AkramHourani/MapperBot/HardwareDesign/Schematic/slamcAR01.sch

## EAGLE design HardwareDesign/Schematic/slamcAR01.sch (2019-04-01)

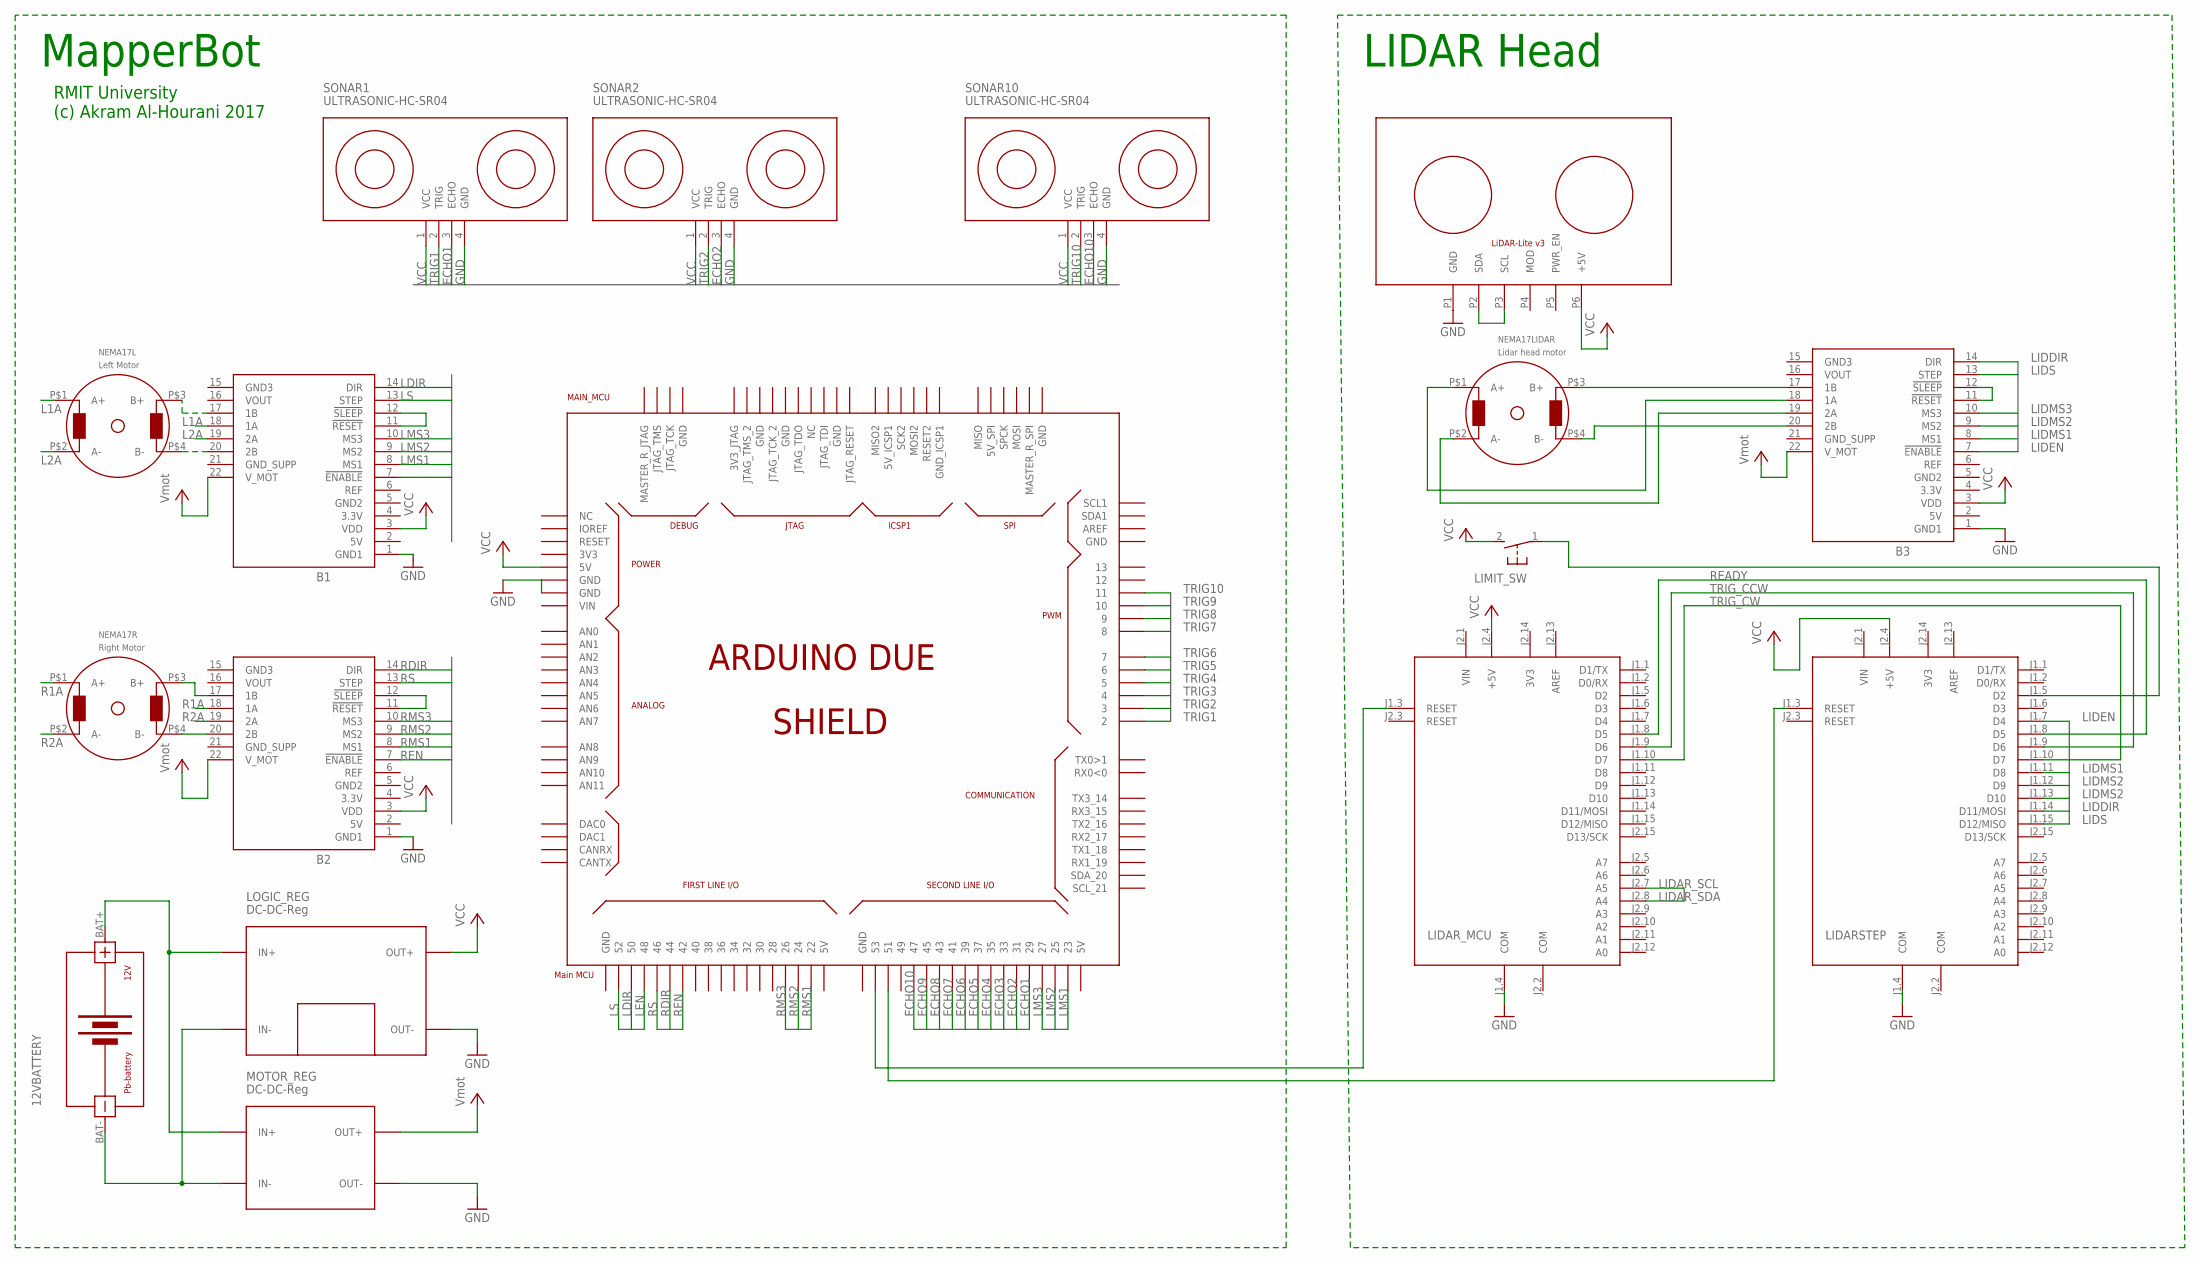
[picture p2: schematic slamcAR01.sch]

Parts:
12VBATTERY: BATTERY-LI-MH12210
B1, B2, B3: POLOLU_1183
LIDARSTEP: ARDUINO_NANO2
LIDAR_MCU: ARDUINO_NANO2
LIMIT_SW: 31-XX; B3F-31XX
LOGIC_REG: DC-DC-Reg; DC-DC-LM2596-DISP
MAIN_MCU: Main MCU; ARDUINO_DUE_SHIELD
MOTOR_REG: DC-DC-Reg; DC-DC-STEP-DOWN-LM2596
NEMA17L: Left Motor; X25_168
NEMA17LIDAR: Lidar head motor; X25_168
NEMA17R: Right Motor; X25_168
SONAR1, SONAR2, SONAR10: ULTRASONIC-HC-SR04
U$6: LIDAR

Connections:
ECHO1: MAIN_MCU.29, SONAR1.3 (ECHO)
ECHO2: MAIN_MCU.31, SONAR2.3 (ECHO)
ECHO3: MAIN_MCU.33
ECHO4: MAIN_MCU.35
ECHO5: MAIN_MCU.37
ECHO6: MAIN_MCU.39
ECHO7: MAIN_MCU.41
ECHO8: MAIN_MCU.43
ECHO9: MAIN_MCU.45
ECHO10: MAIN_MCU.47, SONAR10.3 (ECHO)
GND: B2.1 (GND1), B3.1 (GND1), LIDARSTEP.J1.4 (COM), LIDAR_MCU.J1.4 (COM), LOGIC_REG.OUT-, MAIN_MCU.GND, MAIN_MCU.GND_1 (GND), MOTOR_REG.OUT-, SONAR1.4 (GND), SONAR2.4 (GND), SONAR10.4 (GND), U$6.P1 (GND)
L1A: B1.18 (1A), NEMA17L.P$1 (A+)
L2A: B1.19 (2A), NEMA17L.P$2 (A-)
LDIR: B1.14 (DIR), MAIN_MCU.50
LEN: B1.7 (!ENABLE), MAIN_MCU.48
LIDAR_SCL: LIDAR_MCU.J2.7 (A5)
LIDAR_SDA: LIDAR_MCU.J2.8 (A4), U$6.P2 (SDA), U$6.P3 (SCL)
LIDDIR: B3.14 (DIR), LIDARSTEP.J1.14 (D11/MOSI)
LIDEN: B3.7 (!ENABLE), LIDARSTEP.J1.7 (D4)
LIDMS1: B3.8 (MS1), LIDARSTEP.J1.11 (D8)
LIDMS2: B3.9 (MS2), LIDARSTEP.J1.12 (D9), LIDARSTEP.J1.13 (D10)
LIDMS3: B3.10 (MS3)
LIDS: B3.13 (STEP), LIDARSTEP.J1.15 (D12/MISO)
LMS1: B1.8 (MS1), MAIN_MCU.23
LMS2: B1.9 (MS2), MAIN_MCU.25
LMS3: B1.10 (MS3), MAIN_MCU.27
LS: B1.13 (STEP), MAIN_MCU.52
unnamed: B1.17 (1B), NEMA17L.P$3 (B+)
unnamed: B1.20 (2B), NEMA17L.P$4 (B-)
unnamed: B2.17 (1B), NEMA17R.P$3 (B+)
unnamed: B2.20 (2B), NEMA17R.P$4 (B-)
unnamed: B1.11 (!RESET), B1.12 (!SLEEP)
unnamed: B2.11 (!RESET), B2.12 (!SLEEP)
unnamed: LIDAR_MCU.J1.3 (RESET), MAIN_MCU.53
unnamed: LIDARSTEP.J1.3 (RESET), MAIN_MCU.51
unnamed: B3.17 (1B), NEMA17LIDAR.P$3 (B+)
unnamed: B3.20 (2B), NEMA17LIDAR.P$4 (B-)
unnamed: B3.19 (2A), NEMA17LIDAR.P$2 (A-)
unnamed: B3.18 (1A), NEMA17LIDAR.P$1 (A+)
unnamed: B3.11 (!RESET), B3.12 (!SLEEP)
unnamed: LIDARSTEP.J1.5 (D2), LIMIT_SW.1
unnamed: 12VBATTERY.BAT+, LOGIC_REG.IN+, MOTOR_REG.IN+
unnamed: 12VBATTERY.BAT-, LOGIC_REG.IN-, MOTOR_REG.IN-
R1A: B2.18 (1A), NEMA17R.P$1 (A+)
R2A: B2.19 (2A), NEMA17R.P$2 (A-)
RDIR: B2.14 (DIR), MAIN_MCU.44
READY: LIDARSTEP.J1.8 (D5), LIDAR_MCU.J1.8 (D5)
REN: B2.7 (!ENABLE), MAIN_MCU.42
RMS1: B2.8 (MS1), MAIN_MCU.22
RMS2: B2.9 (MS2), MAIN_MCU.24
RMS3: B2.10 (MS3), MAIN_MCU.26
RS: B2.13 (STEP), MAIN_MCU.46
TRIG1: MAIN_MCU.2, SONAR1.2 (TRIG)
TRIG2: MAIN_MCU.3, SONAR2.2 (TRIG)
TRIG3: MAIN_MCU.4
TRIG4: MAIN_MCU.5
TRIG5: MAIN_MCU.6
TRIG6: MAIN_MCU.7
TRIG7: MAIN_MCU.8
TRIG8: MAIN_MCU.9
TRIG9: MAIN_MCU.10
TRIG10: MAIN_MCU.11, SONAR10.2 (TRIG)
TRIG_CCW: LIDARSTEP.J1.9 (D6), LIDAR_MCU.J1.9 (D6)
TRIG_CW: LIDARSTEP.J1.10 (D7), LIDAR_MCU.J1.10 (D7)
VCC: B1.3 (VDD), B1.22 (V_MOT), B2.3 (VDD), B2.22 (V_MOT), B3.3 (VDD), B3.22 (V_MOT), LIDARSTEP.J2.4 (+5V), LIDAR_MCU.J2.4 (+5V), LIMIT_SW.2 (S), LOGIC_REG.OUT+, MAIN_MCU.5V0 (5V), MOTOR_REG.OUT+, SONAR1.1 (VCC), SONAR2.1 (VCC), SONAR10.1 (VCC), U$6.P6 (+5V)

Notes on the sheet:
MapperBot
RMIT University (c) Akram Al-Hourani 2017
LIDAR Head
